shebeko79/robocart/src/motor_speed .cpp

#include "motor_speed.h"

//st=4 0;0;1
//st=6 0;1;1
//st=2 0;1;0
//st=3 1;1;0
//st=1 1;0;0
//st=5 1;0;1
static constexpr int hall2idx[]={-1,4,2,3,0,5,1,-1};

  void MotorSpeed::speed_pin_isr()
{
  int hall_idx = readHallIndex();

  //Incorrect state of hall sensors
  if(hall_idx == -1)
    return;

  int d = hall_idx - m_hall_idx;
  if(std::abs(d)>3)
    d += 6*(d<0) -6*(d>0);

  m_hall_idx = hall_idx;

  unsigned t = m_timer_val;
  m_periods[t%PERIODS_COUNT] += d;
  m_ticks_count += d;
}

int MotorSpeed::readHallIndex()
{
  unsigned st = (digitalRead(m_hall_a) == HIGH) | ((digitalRead(m_hall_b) == HIGH)<<1) | ((digitalRead(m_hall_c) == HIGH)<<2);
  return hall2idx[st];
}

void MotorSpeed::timer_isr(unsigned timer_val)
{
  unsigned new_pi=timer_val%PERIODS_COUNT;
  unsigned old_pi=m_timer_val%PERIODS_COUNT;

  if(new_pi != old_pi)
  {
    m_ticks_count-=m_periods[new_pi];
    m_periods[new_pi] = 0;
  }

  m_timer_val = timer_val;
}

void MotorSpeed::apply()
{
  float cur_speed = get_speed_meters();
  Motor::State st = m_motor.get_state();

  if(st == Motor::st_brake && m_brake_state == bs_change_direction)
  {
    if(std::abs(cur_speed)>OFF_SPEED)
      return;
    
    m_motor.soft_stop();
    cur_speed = 0.0;
    // Serial.println("after brake off");
  }

  if(st==Motor::st_forward && m_dst_speed<-OFF_SPEED ||
      st==Motor::st_backward && m_dst_speed>OFF_SPEED)
  {
    // Serial.println("brake");
    m_motor.brake();
    m_brake_state = bs_change_direction;
    reset_pid();
    return;
  }

  if(m_dst_speed==0.0)
  {
    m_motor.brake();
    m_brake_state = bs_zero_speed;
    reset_pid();
    return;
  }

  bool is_brake = false;
  float ctl_pwm=calc_pwm(cur_speed,is_brake);
  if(is_brake)
  {
    m_motor.brake();
    m_brake_state = bs_speed_compensation;
    return;
  }

  int pwm = ctl_pwm*Motor::MAX_PWM;
  pwm = constrain(pwm, -Motor::MAX_PWM, Motor::MAX_PWM);

  if(pwm<0)
    m_motor.backward(-pwm);
  else
    m_motor.forward(pwm);
}

float MotorSpeed::calc_pwm(float cur_speed, bool &is_brake)
{
  unsigned long cur_time = millis();
  float cur_acc = 0.0;

  float res;
  float kick = 0.0;

  if(m_prev_steps < 2)
  {
    res = m_speed2pwm * m_dst_speed;
    ++m_prev_steps;
  }
  else
  {
    float cur_delay;
    if(cur_time == m_prev_time)
      cur_delay=EXPECTED_PWM_DELAY;
    else
      cur_delay = (cur_time - m_prev_time)/1000.0;
    
    cur_acc = (cur_speed-m_prev_speed)/cur_delay;
    const float kdirection = (m_dst_speed<0)? -1.0:1.0;
    const float dx = (cur_speed*kdirection<=m_dst_speed*kdirection)? 1.0:-1.0;
    const float speed_correction = dx*kdirection>0? UP_SPEED_CORRECTION:DOWN_SPEED_CORRECTION;

    res = m_prev_pwm;

    if(cur_acc*dx*kdirection<0.0 || cur_acc*dx*kdirection<CLOSE_TO_ZERO_ACCELERATION)
    {
      res = m_prev_pwm+(m_dst_speed-cur_speed)*speed_correction;
    }

    if(dx>0)
    {
      if(m_prev_acc == 0.0 && cur_acc==0.0 && cur_speed == 0.0 && std::abs(m_dst_speed)>CLOSE_TO_ZERO_SPEED_DIFF)
         kick = KICK_PWM_CORRECTION*kdirection;
    }
    else
    {
      if(cur_acc*kdirection>CLOSE_TO_ZERO_ACCELERATION && (cur_speed-m_dst_speed)*kdirection>BREAK_MAX_SPEED_DIFF_WITH_ACCELERATION || (cur_speed-m_dst_speed)*kdirection>BREAK_MAX_SPEED_DIFF)
      {
        is_brake=true;
        res -= BREAK_PWM_CORRECTION*kdirection;
      }
    }

    res = constrain(res, -1.0, 1.0);
    

    // Serial.print(" dst_sp=");
    // Serial.print(m_dst_speed,4);
    // Serial.print(" cur_sp=");
    // Serial.print(cur_speed,4);
    // Serial.print(" acc=");
    // Serial.print(cur_acc,4);
    // Serial.print(" prev_acc=");
    // Serial.print(m_prev_acc,4);
    // Serial.print(" new_pwm=");
    // Serial.print(res,4);
    // Serial.print(" prev_pwm=");
    // Serial.print(m_prev_pwm,4);
    // Serial.print(" speed2pwm=");
    // Serial.print(m_speed2pwm,4);
    // Serial.println("");
  }

  m_prev_speed=cur_speed;
  m_prev_acc = cur_acc;
  m_prev_time=cur_time;
  m_prev_pwm = res;

  res += kick;
  res = constrain(res, -1.0, 1.0);
  
  return  res;
}

void MotorSpeed::reset_pid()
{
  m_prev_steps = 0;
  m_prev_speed = 0.0;
  m_prev_time = 0;
  m_prev_acc = 0.0;
  m_prev_pwm = 0.0;
}

void MotorSpeed::fail_safe()
{
  m_dst_speed = 0.0;
  m_motor.brake();
  m_brake_state = bs_fail_safe;
  reset_pid();
}

void MotorSpeed::dump_state(const String& caption, Stream& stream)
{
  float cur_speed = get_speed_meters();
  Motor::State st = m_motor.get_state();

  if(st == Motor::st_brake && cur_speed == 0.0)
  {
    return;
  }

  stream.print(caption);
  stream.print(":");
  stream.print(" time=");
  stream.print(millis());
  stream.print(" dst_speed=");
  stream.print(abs(m_dst_speed),4);
  stream.print(" cur_speed=");
  stream.print(cur_speed,4);
  stream.print(" PWM=");
  stream.print(m_prev_pwm,4);
  stream.print(" speed2pwm=");
  stream.print(m_speed2pwm,4);
  stream.println("");
}
