shebeko79/robocart/maix/states.py

import math

from maix import image, app

import algos
import pan_tilt
import tracker
import mover
import track_utils


class Button:
    def __init__(self, caption, state_name=None, enabled=True):
        self.caption = caption
        self.state_name = state_name
        self.enabled = enabled


class BaseState:
    state_name = "base"

    rectangle_cap = "Select rectangle"
    click_cap = "Select tracker"
    rectangle_color = image.Color.from_rgb(255, 0, 0)
    info_color = image.Color.from_rgb(0, 128, 0)

    def __init__(self):
        self.buttons = []
        self.accept_rectangle = False
        self.accept_click = False
        self.accept_user_move = True
        self.accept_user_move_cam = True

    def draw_screen(self, cam_img: image.Image, out_size):
        img = cam_img.resize(out_size[0], out_size[1])

        if self.accept_rectangle:
            img.draw_string(2, 4, self.rectangle_cap,
                            self.rectangle_color, 1.5)
        else:
            tracker.draw_trackers(img)

        if self.accept_click:
            img.draw_string(2, 4, self.click_cap,
                            self.rectangle_color, 1.5)

        self.draw_voltage(img)
        self.draw_buttons(img)

        return img

    def enter(self):
        self.buttons = []

    def leave(self):
        pass

    def process(self):
        pass

    def on_click(self, pt):
        pass

    def on_rectangle(self, cam_img: image.Image, rc):
        pass

    def on_click_button(self, btn: Button):
        if btn.state_name:
            set_state(btn.state_name)

    def hit_test(self, pt):
        for btn in self.buttons:
            if not btn.enabled:
                continue

            rc = btn.rc
            if not rc:
                continue

            if rc[0] < pt[0] < rc[2] and rc[1] < pt[1] < rc[3]:
                return btn
        return None

    def button_by_name(self, caption):
        for btn in self.buttons:
            if btn.caption == caption:
                return btn

        return None

    def draw_voltage(self, img: image.Image):
        voltage_str = f"{mover.voltage:.1f}V"
        font_size = image.string_size(voltage_str, font="sans")
        img.draw_string(img.width() - int(font_size[0]*0.75), 4, voltage_str, self.info_color, 0.75, font="sans")

    def draw_buttons(self, img: image.Image):
        indent = 8
        enabled_cl = image.Color.from_rgb(255, 255, 255)
        disabled_cl = image.Color.from_rgb(127, 127, 127)

        x = 0
        for btn in self.buttons:
            cl = enabled_cl
            if not btn.enabled:
                cl = disabled_cl

            font_size = image.string_size(btn.caption, font="sans")
            rect_w = font_size[0] + indent * 2
            rect_h = font_size[1] + indent * 2

            btn.rc = [x, img.height() - rect_h, x + rect_w, img.height()]

            img.draw_rect(x, img.height() - rect_h, rect_w, rect_h, cl, 4)
            img.draw_string(x + (rect_w - font_size[0]) // 2, img.height() - rect_h + (rect_h - font_size[1]) // 2,
                            btn.caption, cl, 1, font="sans")

            x += rect_w + indent


current_state: BaseState = None
states = {}


def add_state(state):
    states[state.state_name] = state


def set_state(state_name):
    global current_state
    global states

    if not (state_name in states):
        print(f"state {state_name} doesn't exist")
        return

    new_state = states[state_name]

    if current_state:
        current_state.leave()

    current_state = new_state
    new_state.enter()
    print(f"new state: {state_name}")


class MainState(BaseState):
    state_name = "main"

    def enter(self):
        self.buttons = [Button("Points", PointsState.state_name),
                        Button("Track", TrackSelectState.state_name),
                        Button("Move", MoveState.state_name),
                        Button("Pan", PanTiltState.state_name)
                        #, Button("Exit", ExitState.state_name)
                        ]


class PointsState(BaseState):
    state_name = "points"

    def enter(self):
        self.buttons = [Button("Add", AddPointState.state_name),
                        Button("DelLast", DeleteLastPointState.state_name, tracker.nanotrack_count() > 0),
                        Button("Back", MainState.state_name)]


class ExitState(BaseState):
    state_name = "exit"

    def enter(self):
        app.set_exit_flag(True)


class AddPointState(BaseState):
    state_name = "add_point"

    def __init__(self):
        super().__init__()
        self.accept_rectangle = True

    def enter(self):
        self.buttons = []

    def on_rectangle(self, cam_img: image.Image, rc):
        if rc[2]-rc[0] == 0 or rc[3] - rc[1] == 0:
            return

        tracker.add_nanotracker(cam_img, rc)
        set_state(PointsState.state_name)


class DeleteLastPointState(BaseState):
    state_name = "delete_last_point"

    def enter(self):
        tracker.remove_lastnanotrack()
        set_state(PointsState.state_name)


class TrackSelectState(BaseState):
    state_name = "track_select"

    def enter(self):
        self.buttons = [Button("PanTo", TrackInitState.state_name),
                        Button("MoveTo", MoveToSelectTrackerState.state_name),
                        Button("Follow", FollowInitState.state_name),
                        Button("Back", MainState.state_name)
                        ]


class TrackInitState(BaseState):
    state_name = "track_init"

    def __init__(self):
        super().__init__()
        self.accept_click = True
        self.fit = None
        self.do_pan = True
        self.do_move = False
        self.continues = True

    def move_to(self, tr):
        alg = algos.MoveToAlgo(tr, self.fit, self.do_pan, self.do_move, self.continues)
        algos.set_algo(alg)
        set_state(TrackState.state_name)

    def enter(self):
        self.buttons = [Button("Back", MainState.state_name)]

    def on_click(self, pt):
        tr = tracker.hit_test(pt)
        if tr:
            self.move_to(tr)


class FollowInitState(TrackInitState):
    state_name = "follow_init"

    def __init__(self):
        super().__init__()
        self.do_move = True


class TrackState(BaseState):
    state_name = "track"

    def __init__(self):
        super().__init__()
        self.accept_user_move = False
        self.accept_user_move_cam = False

    def enter(self):
        self.buttons = [Button("Stop", MainState.state_name)]

    def leave(self):
        algos.set_algo(None)

    def process(self):
        if algos.current_algo is None or algos.current_algo.is_stopped():
            set_state(MainState.state_name)


class MoveToSelectTrackerState(BaseState):
    state_name = "move_to_select_tracker"

    def __init__(self):
        super().__init__()
        self.accept_click = True

    def enter(self):
        self.buttons = [Button("Back", MainState.state_name)]

    def on_click(self, pt):
        tr = tracker.hit_test(pt)
        if tr:
            MoveToSelectFitState.tr = tr
            set_state(MoveToSelectFitState.state_name)


class MoveToSelectFitState(TrackInitState):
    state_name = "move_to_select_fit"
    tr = None

    def __init__(self):
        super().__init__()
        self.accept_click = False
        self.accept_rectangle = True
        self.do_move = True
        self.continues = False
        self.rectangle_cap = "Draw fit size"

    def enter(self):
        self.buttons = [Button("Back", MainState.state_name)]

    def on_rectangle(self, cam_img: image.Image, rc):
        w = abs(rc[2] - rc[0])
        h = abs(rc[3] - rc[1])

        if w == 0 or h == 0:
            return

        fit = max(w, h)
        if fit > 1.0:
            fit = 1.0

        tr_fit = algos.get_fit(self.tr)

        if fit > tr_fit:
            self.fit = fit
            self.move_to(self.tr)

    def leave(self):
        MoveToSelectFitState.tr = None


class MoveState(BaseState):
    state_name = "move"

    def __init__(self):
        super().__init__()

    def enter(self):
        self.buttons = [Button("D"), Button("<<"), Button(">>"), Button("R"), Button("Stop"),
                        Button("Back", MainState.state_name)]

    def leave(self):
        mover.stop()

    def on_click_button(self, btn: Button):
        if btn.state_name:
            set_state(btn.state_name)
            return

        if btn.caption == "Stop":
            mover.stop()
            return

        speed = 0
        pan = 0

        if btn.caption == "<<":
            pan = -1
        elif btn.caption == ">>":
            pan = 1
        elif btn.caption == "D":
            speed = 1
        elif btn.caption == "R":
            speed = -1
        else:
            return

        mover.distance(speed, pan, track_utils.MOVE_DISTANCE)


class PanTiltState(BaseState):
    state_name = "pan_tilt"
    MOVE_ANGLE = 5/180.0*math.pi

    def __init__(self):
        super().__init__()

    def enter(self):
        self.buttons = [Button("U"), Button("<"), Button(">"), Button("D"),
                        Button("F"), Button("B"), Button("T"), Button("L"), Button("R"), Button("Fr"),
                        Button("Bck", MainState.state_name)]

    def leave(self):
        pan_tilt.release()

    def on_click_button(self, btn: Button):
        if btn.state_name:
            set_state(btn.state_name)
        elif btn.caption == "U":
            v = pan_tilt.get_tilt_angle()
            pan_tilt.set_tilt_angle(v-self.MOVE_ANGLE)
        elif btn.caption == "<":
            v = pan_tilt.get_pan_angle()
            pan_tilt.set_pan_angle(v-self.MOVE_ANGLE)
        elif btn.caption == ">":
            v = pan_tilt.get_pan_angle()
            pan_tilt.set_pan_angle(v+self.MOVE_ANGLE)
        elif btn.caption == "D":
            v = pan_tilt.get_tilt_angle()
            pan_tilt.set_tilt_angle(v+self.MOVE_ANGLE)
        elif btn.caption == "F":
            pan_tilt.set_pan(pan_tilt.Pan.CENTER)
            pan_tilt.set_tilt(pan_tilt.Tilt.FRONT)
        elif btn.caption == "B":
            pan_tilt.set_pan(pan_tilt.Pan.CENTER)
            pan_tilt.set_tilt(pan_tilt.Tilt.BACKWARD)
        elif btn.caption == "T":
            pan_tilt.set_pan(pan_tilt.Pan.CENTER)
            pan_tilt.set_tilt(pan_tilt.Tilt.UP)
        elif btn.caption == "L":
            pan_tilt.set_pan(pan_tilt.Pan.LEFT)
            pan_tilt.set_tilt(pan_tilt.Tilt.FRONT)
        elif btn.caption == "R":
            pan_tilt.set_pan(pan_tilt.Pan.RIGHT)
            pan_tilt.set_tilt(pan_tilt.Tilt.FRONT)
        elif btn.caption == "Fr":
            pan_tilt.release()


def init():
    add_state(MainState())
    add_state(PointsState())
    add_state(AddPointState())
    add_state(DeleteLastPointState())
    add_state(TrackSelectState())
    add_state(TrackInitState())
    add_state(FollowInitState())
    add_state(TrackState())
    add_state(MoveToSelectTrackerState())
    add_state(MoveToSelectFitState())
    add_state(MoveState())
    add_state(PanTiltState())
    add_state(ExitState())
