shebeko79/robocart/maix/udp_server.py

from maix import image, time
import socket
import select
from packet_processor import PacketProcessor, PacketType
import aes_pack

import mover
import pan_tilt
import states
import track_utils
import tracker

UDP_PORT = 5005
STATE_SEND_PERIOD = 5000
CONNECTION_EXPIRE_TIMEOUT = 60
GET_ADDRESS_TIMEOUT = 60
MIN_JPEG_QUALITY = 5
DOWNSCALE_JPEG_QUALITY = 35
UPSCALE_JPEG_QUALITY = 55
MAX_JPEG_QUALITY = 75


class UdpConnection(PacketProcessor):
    def __init__(self, key=None):
        super().__init__()

        self.img_no_ack_timeout = 3000
        self.expected_jpeg_size = 40000

        self.img: image.Image = None
        self.require_state_answer = False
        self.jpeg_quality = 50

        self.last_received_addr = None
        self.last_received_packet_number = 0

        self.last_ack_packet_number = 0

        self.last_image_packet = 0
        self.last_image_send_time = 0
        self.last_state_send_time = 0
        self.last_received_time = time.time_s()
        self.packets = []

        self.is_image_timeout = False
        self.is_rescale_image = False

        if key is not None:
            self.aes = aes_pack.AesPack(key)
            self.is_crypted = True

    def process(self, img):
        self.do_receive()
        self.do_send(img)

    def reset_peer(self):
        #print('reset_peer()')
        self.last_received_addr = None
        self.last_received_packet_number = 0

        self.last_ack_packet_number = 0

        self.last_image_packet = 0
        self.last_image_send_time = 0
        self.last_state_send_time = 0
        self.last_received_time = time.time_s()
        self.packets = []

    def is_connection_expired(self):
        tm = time.time_s()
        return tm > self.last_received_time + CONNECTION_EXPIRE_TIMEOUT

    def do_receive(self):
        sel = select.select([self.sock], [], [self.sock], 0)

        if len(sel[2]) != 0:
            print('UdpConnection.do_receive() socket error')
            return

        if len(sel[0]) == 0:
            if self.is_connection_expired():
                self.reset_peer()
            return

        data, addr = self.sock.recvfrom(65535)
        pack_n = self.get_packet_number(data)
        if pack_n is None:
            return

        #print(f'do_receive()1: {addr=} {self.last_received_addr} {len(data)=} {pack_n=} {self.last_received_packet_number=}')
        if self.last_received_addr is None or self.last_received_addr != addr:
            self.reset_peer()
            self.last_received_addr = addr
            self.last_received_packet_number = pack_n
        elif self.is_packet_too_old(pack_n):
            return

        if self.parse(data):
            self.last_received_time = time.time_s()
            track_utils.last_request_time = self.last_received_time
            self.last_received_packet_number = pack_n

    def do_send(self, img):
        if self.last_received_addr is None:
            return

        sel = select.select([], [self.sock], [self.sock], 0)

        if len(sel[2]) != 0:
            print('UdpConnection.do_send() socket error')
            return

        if len(sel[1]) == 0:
            return

        is_ready_to_send = True

        if len(self.packets) > 0:
            bts = self.pack()
            self.sock.sendto(bts, self.last_received_addr)

            sel = select.select([], [self.sock], [self.sock], 0)

            if len(sel[2]) != 0:
                print('UdpServer.do_send() socket error after sending')
                return

            is_ready_to_send = len(sel[1]) > 0

        tm = time.time_ms()
        self.img = img
        self.is_image_timeout = tm >= self.last_image_send_time + self.img_no_ack_timeout

        is_send_image = self.img is not None and is_ready_to_send and len(self.packets) == 0 and \
                        not self.is_connection_expired() and \
                        (self.last_ack_packet_number >= self.last_image_packet or self.is_image_timeout)

        #print(f'{is_send_image}: {is_ready_to_send} {len(self.packets)=} {tm=} {self.last_image_send_time=} {self.last_ack_packet_number=} {self.last_image_packet=} {self.send_packet_number=} {self.send_partial_offset=}')
        if is_send_image:
            pck = self.pack_img()
            if pck is not None:
                self.last_image_packet = self.get_next_packet_number()
                self.last_image_send_time = tm
                self.packets.append(pck)
                #print(f'send_image: image_timeout={self.is_image_timeout} len={len(pck[1])} {self.last_ack_packet_number=} {self.last_image_packet=}')

        if self.require_state_answer or tm >= self.last_state_send_time + STATE_SEND_PERIOD:
            #print(f'do_send() send state: {self.require_state_answer=} {tm=} {self.last_state_send_time=}')
            pck = self.pack_state()
            if pck is not None:
                self.require_state_answer = False
                self.last_state_send_time = tm
                self.packets.append(pck)

        while is_ready_to_send and len(self.packets) > 0:
            bts = self.pack()
            ret = self.sock.sendto(bts, self.last_received_addr)
            #print(f'do_send(): {len(bts)=} {self.last_received_addr=} {ret=}')
            if ret != len(bts):
                break

            sel = select.select([], [self.sock], [self.sock], 0)

            if len(sel[2]) != 0:
                print('UdpServer.do_send() socket error after sending')
                break

            is_ready_to_send = len(sel[1]) > 0

            if is_ready_to_send and len(self.packets) > 0:
                time.sleep_ms(10)

    def pack_img(self) -> bytes:
        if not self.img:
            return None

        if self.is_image_timeout:
            self.jpeg_quality -= 1
            if self.jpeg_quality < MIN_JPEG_QUALITY:
                self.jpeg_quality = MIN_JPEG_QUALITY
            #print(f'pack_img() decrease quality by timeout: {self.jpeg_quality=}')

        if self.jpeg_quality < DOWNSCALE_JPEG_QUALITY:
            self.is_rescale_image = True
        elif self.jpeg_quality > UPSCALE_JPEG_QUALITY:
            self.is_rescale_image = False

        if self.is_rescale_image:
            img = self.img.resize(self.img.width()//2, self.img.height()//2)
            #print(f'pack_img() rescale to ({img.width()},{img.height()})')
        else:
            img = self.img.copy()

        if not img:
            return None

        tracker.draw_trackers(img)

        jpg = img.to_jpeg(self.jpeg_quality)
        if not jpg:
            return None

        bts = jpg.to_bytes()
        len_bts = len(bts)

        if len_bts > self.expected_jpeg_size:
            self.jpeg_quality -= 1
            if self.jpeg_quality < MIN_JPEG_QUALITY:
                self.jpeg_quality = MIN_JPEG_QUALITY
            #print(f'pack_img() decrease quality by size: {len(bts)=} {self.jpeg_quality=}')
        elif len_bts < self.expected_jpeg_size and not self.is_image_timeout:
            self.jpeg_quality += 1
            if self.jpeg_quality > MAX_JPEG_QUALITY:
                self.jpeg_quality = MAX_JPEG_QUALITY
            #print(f'pack_img() increase quality by size: {len(bts)=} {self.jpeg_quality=}')

        return self.pack_chunk(jpg.to_bytes(), PacketType.JPG)

    def pack_state(self) -> bytes:
        st = states.current_state
        cur_state = {}

        if st is not None:
            cur_state['state_name'] = st.state_name
            cur_state['accept_click'] = st.accept_click
            cur_state['accept_rectangle'] = st.accept_rectangle
            cur_state['rectangle_cap'] = st.rectangle_cap
            cur_state['click_cap'] = st.click_cap
            cur_state['voltage'] = mover.voltage

            buttons = []
            for b in st.buttons:
                buttons.append({'caption': b.caption, 'enabled': b.enabled})
            cur_state['buttons'] = buttons

        return self.pack_json(cur_state)

    def crypt(self, bts):
        ret = self.aes.crypt(bts)
        return ret

    def decrypt(self, bts, packet_number):
        return self.aes.decrypt(bts)

    def process_ack(self, ack_packet_number):
        self.last_ack_packet_number = ack_packet_number
        pass

    def process_json(self, js):
        if 'cmd' not in js:
            return

        cmd = js['cmd']

        if cmd == "click":
            self.click(js)
        elif cmd == "click_point":
            self.click_point(js)
        elif cmd == "sel_rect":
            self.sel_rect(js)
        elif cmd == "move_cam":
            self.move_cam(js)
        elif cmd == "moveto_cam":
            self.moveto_cam(js)
        elif cmd == "move":
            self.move(js)
        elif cmd == "release_cam":
            self.release_cam(js)

    def click(self, js):
        state_name = js['state_name']
        caption = js['caption']
        self.require_state_answer = True

        st = states.current_state
        if st is None or state_name != st.state_name:
            return

        btn = st.button_by_name(caption)
        if btn is not None and btn.enabled:
            st.on_click_button(btn)

    def click_point(self, js):
        state_name = js['state_name']
        x = js['x']
        y = js['y']
        self.require_state_answer = True

        if not (0.0 <= x <= 1.0 and 0.0 <= y <= 1.0):
            raise Exception("Coordinates out of range")

        st = states.current_state
        if st is None or state_name != st.state_name:
            return

        if st.accept_click:
            st.on_click([x, y])

    def sel_rect(self, js):
        state_name = js['state_name']
        x1 = js['x1']
        y1 = js['y1']
        x2 = js['x2']
        y2 = js['y2']
        self.require_state_answer = True

        if not (0.0 <= x1 <= 1.0 and 0.0 <= y1 <= 1.0 and 0.0 <= x2 <= 1.0 and 0.0 <= y2 <= 1.0):
            raise Exception("Coordinates out of range")

        st = states.current_state
        if st is None or state_name != st.state_name:
            return

        if st.accept_rectangle and self.img:
            rc = track_utils.make_rect([x1, y1], [x2, y2])
            st.on_rectangle(self.img, rc)

    def move_cam(self, js):
        pan = js['pan']
        tilt = js['tilt']
        self.require_state_answer = True

        st = states.current_state
        if st is None or not st.accept_user_move_cam:
            return

        p = pan_tilt.get_pan_angle()
        t = pan_tilt.get_tilt_angle()

        p = p + pan
        t = t + tilt

        pan_tilt.set_pan_angle(p)
        pan_tilt.set_tilt_angle(t)

    def moveto_cam(self, js):
        pan = js['pan']
        tilt = js['tilt']
        self.require_state_answer = True

        st = states.current_state
        if st is None or not st.accept_user_move_cam:
            return

        if not isinstance(pan, str):
            pan = pan_tilt.angle2pan(pan)
        elif pan.upper() == "LEFT":
            pan = pan_tilt.Pan.LEFT
        elif pan.upper() == "RIGHT":
            pan = pan_tilt.Pan.RIGHT
        elif pan.upper() == "CENTER":
            pan = pan_tilt.Pan.CENTER
        elif pan.upper() == "MIN":
            pan = pan_tilt.Pan.MIN
        elif pan.upper() == "MAX":
            pan = pan_tilt.Pan.MAX
        else:
            pan = pan_tilt.get_pan()

        if not isinstance(tilt, str):
            tilt = pan_tilt.angle2tilt(tilt)
        elif tilt.upper() == "BACKWARD":
            tilt = pan_tilt.Tilt.BACKWARD
        elif tilt.upper() == "UP":
            tilt = pan_tilt.Tilt.UP
        elif tilt.upper() == "FRONT":
            tilt = pan_tilt.Tilt.FRONT
        elif tilt.upper() == "MIN":
            tilt = pan_tilt.Tilt.MIN
        elif tilt.upper() == "MAX":
            tilt = pan_tilt.Tilt.MAX
        else:
            tilt = pan_tilt.get_tilt()

        pan_tilt.set_pan(pan)
        pan_tilt.set_tilt(tilt)

    def move(self, js):
        speed = js['speed']
        pan = js['pan']
        self.require_state_answer = True

        st = states.current_state
        if st is None or not st.accept_user_move_cam:
            return

        mover.distance(speed, pan, track_utils.MOVE_DISTANCE)

    def release_cam(self, js):
        self.require_state_answer = True
        pan_tilt.release()


class UdpServer(UdpConnection):
    def __init__(self, sock: socket, key=None):
        super().__init__(key)

        self.set_max_packet_size(45000)

        self.sock = sock
        self.sock.setblocking(False)


class UdpClient(UdpConnection):
    def __init__(self, host_name, port, key=None):
        super().__init__(key)

        self.img_no_ack_timeout = 4000
        self.expected_jpeg_size = 8000

        self.sock: socket.socket = None
        self.host_name = host_name
        self.port = port
        self.addr = None
        self.last_get_address_time = 0
        self.last_received_time = 0

    def process(self, img):
        if not self.sock:
            self.resolve_addr()

        if self.sock:
            try:
                self.do_receive()
                self.do_send(img)
            except Exception as e:
                print(f'process(): {e}')
                self.reset_peer()
                if self.sock:
                    self.sock.close()
                    self.sock = None

    def resolve_addr(self):
        tm = time.time_s()
        if tm < self.last_get_address_time + GET_ADDRESS_TIMEOUT:
            return

        self.last_get_address_time = tm
        try:
            res = socket.getaddrinfo(self.host_name, None)

            r = res[0]
            proto = r[0]
            self.addr = (r[4][0], self.port)

            if self.sock:
                self.sock.close()

            self.sock = socket.socket(proto, socket.SOCK_DGRAM)
            self.sock.setblocking(False)
            self.last_get_address_time = 0
            self.last_received_addr = self.addr
        except Exception as e:
            print(f'resolve_addr: {e}')

    def reset_peer(self):
        tmp_send_time = self.last_state_send_time

        super().reset_peer()
        self.last_received_addr = self.addr
        self.last_received_time = 0
        self.last_state_send_time = tmp_send_time
