shebeko79/robocart/maix/tracker.py

import math
from maix import nn, image

import track_utils
from track_utils import CAM_SIZE

NANO_MODEL_PATH = "/root/models/nanotrack.mud"

yolo_model = nn.YOLO11(model="/root/models/yolo11n_320_room.mud")
yolo_objects = []
yolo_trackers = []
YOLO_CONFIDENT = 0.8

nanotrack_objects = []


class TrackObject:

    def is_locked(self):
        return False

    def center(self):
        return [0, 0]

    def size(self):
        return [0, 0]

    def start_track(self):
        pass

    def stop_track(self):
        pass

class NanoTrackObject(TrackObject):

    def __init__(self, img: image.Image, rc):
        self.model = nn.NanoTrack(NANO_MODEL_PATH)
        self.model.init(img, rc[0], rc[1], rc[2] - rc[0], rc[3] - rc[1])
        self.rc = rc
        self.img_size = [img.width(), img.height()]
        self.r = self.model.track(img)

    def track(self, img: image.Image):
        self.r = self.model.track(img)

    def is_locked(self):
        return self.r.score > 0.93

    def center(self):
        return [self.r.x + self.r.w / 2, self.r.y + self.r.h / 2]

    def size(self):
        return [self.r.w, self.r.h]


class YoloTrackObject(TrackObject):

    def __init__(self, obj: nn.Object):
        self.class_id = obj.class_id
        self.x = obj.x
        self.y = obj.y
        self.w = obj.w
        self.h = obj.h
        self.score = obj.score

    def track(self, objects):
        sel = None
        sel_d = 0.0
        sel_confident = False
        for o in objects:
            if o.class_id != self.class_id:
                continue

            dx = self.x - o.x
            dy = self.y - o.y
            d = dx*dx + dy*dy
            confident = o.score >= YOLO_CONFIDENT

            if sel is None or d < sel_d or (confident and not sel_confident):
                sel = o
                sel_d = d
                sel_confident = confident

        if sel:
            self.update(sel)
        else:
            self.score = 0.0

    def update(self, obj: nn.Object):
        self.x = obj.x
        self.y = obj.y
        self.w = obj.w
        self.h = obj.h
        self.score = obj.score

    def is_locked(self):
        return self.score > 0.0

    def center(self):
        return [(self.x+self.w/2)/yolo_model.input_width()*CAM_SIZE[0],
                (self.y+self.h/2)/yolo_model.input_height()*CAM_SIZE[1]]

    def size(self):
        return [self.w/yolo_model.input_width()*CAM_SIZE[0],
                self.h/yolo_model.input_height()*CAM_SIZE[1]]

    def start_track(self):
        yolo_trackers.append(self)

    def stop_track(self):
        if self in yolo_trackers:
            yolo_trackers.remove(self)


def add_nanotracker(img, rc):
    rc[0] = int(rc[0] * CAM_SIZE[0])
    rc[1] = int(rc[1] * CAM_SIZE[1])
    rc[2] = int(rc[2] * CAM_SIZE[0])
    rc[3] = int(rc[3] * CAM_SIZE[1])

    nano_img = img
    if nano_img.format() != image.Format.FMT_BGR888:
        nano_img = nano_img.to_format(image.Format.FMT_BGR888)

    tr = NanoTrackObject(nano_img, rc)
    nanotrack_objects.append(tr)


def get_camera_format():
    return image.Format.FMT_RGB888


def draw_trackers(img: image.Image):
    iw = img.width()
    ih = img.height()
    hi_cl = image.Color.from_rgb(255, 0, 0)
    gray_cl = image.Color.from_rgb(127, 127, 127)

    for i in range(0, len(nanotrack_objects)):
        o: TrackObject = nanotrack_objects[i]
        r = o.r

        x = int(r.x * iw / CAM_SIZE[0])
        y = int(r.y * ih / CAM_SIZE[1])
        w = int(r.w * iw / CAM_SIZE[0])
        h = int(r.h * ih / CAM_SIZE[1])

        if o.is_locked():
            cl = hi_cl
        else:
            cl = gray_cl

        img.draw_rect(x, y, w, h, cl, 2)

        cap = f"{i}"
        font_size = image.string_size(cap)
        img.draw_string(x, y - font_size[1] - 2, cap, cl)

    for o in yolo_objects:
        x = int(o.x * iw / yolo_model.input_width())
        y = int(o.y * ih / yolo_model.input_height())
        w = int(o.w * iw / yolo_model.input_width())
        h = int(o.h * ih / yolo_model.input_height())

        if o.score > YOLO_CONFIDENT:
            cl = hi_cl
        else:
            cl = gray_cl

        img.draw_rect(x, y, w, h, cl, 2)
        cap = yolo_model.labels[o.class_id]
        #print(f'{yolo_model.labels[o.class_id]}: {o.score:.2f}')

        font_size = image.string_size(cap)
        img.draw_string(x, y - font_size[1] - 2, cap, cl)


def hit_test(pt):
    sel = None
    sel_d = 0

    ptx = int(pt[0] * CAM_SIZE[0])
    pty = int(pt[1] * CAM_SIZE[1])

    for o in nanotrack_objects:
        r = o.r
        if r.x < ptx < r.x + r.w and r.y < pty < r.y + r.h:
            c = o.center()
            dx = c[0] - ptx
            dy = c[1] - pty
            d = dx * dx + dy * dy

            if not sel or d < sel_d:
                sel = o
                sel_d = d

    if sel:
        return sel

    for o in yolo_objects:
        x = o.x / yolo_model.input_width()
        y = o.y / yolo_model.input_height()
        w = o.w / yolo_model.input_width()
        h = o.h / yolo_model.input_height()

        if x < pt[0] < x + w and y < pt[1] < y + h:
            dx = x - pt[0]
            dy = y - pt[1]
            d = dx * dx + dy * dy

            if not sel or d < sel_d:
                sel = o
                sel_d = d

    if sel is None:
        return sel

    return YoloTrackObject(sel)


def nanotrack_count():
    return len(nanotrack_objects)


def remove_lastnanotrack():
    if len(nanotrack_objects) > 0:
        nanotrack_objects.pop()


def track(img: image.Image, yolo_img: image.Image):
    global yolo_objects

    if len(nanotrack_objects) > 0:
        nano_img = img
        if nano_img.format() != image.Format.FMT_BGR888:
            nano_img = nano_img.to_format(image.Format.FMT_BGR888)
        for o in nanotrack_objects:
            o.track(nano_img)

    yolo_objects = yolo_model.detect(yolo_img, conf_th=0.5, iou_th=0.45)
    for tr in yolo_trackers:
        tr.track(yolo_objects)


def resize_image_for_yolo_model(img: image.Image):
    yolo_img = img
    if yolo_img.width() != yolo_model.input_width() or yolo_img.height() != yolo_model.input_height():
        yolo_img = img.resize(yolo_model.input_width(), yolo_model.input_height())

    return yolo_img
