shebeko79/robocart/proba/rtsp_read.py

import cv2
cap = cv2.VideoCapture("rtsp://192.168.33.9:8554/live")

while(cap.isOpened()):
    ret, frame = cap.read()
    cv2.imshow('frame', frame)
    if cv2.waitKey(20) & 0xFF == ord('q'):
        break
cap.release()
cv2.destroyAllWindows()
